VincenzoHDR/Placchetta-AM100/Placchetta Finita/WhatsApp Image 2023-08-04 at 15.59.29.jpeg

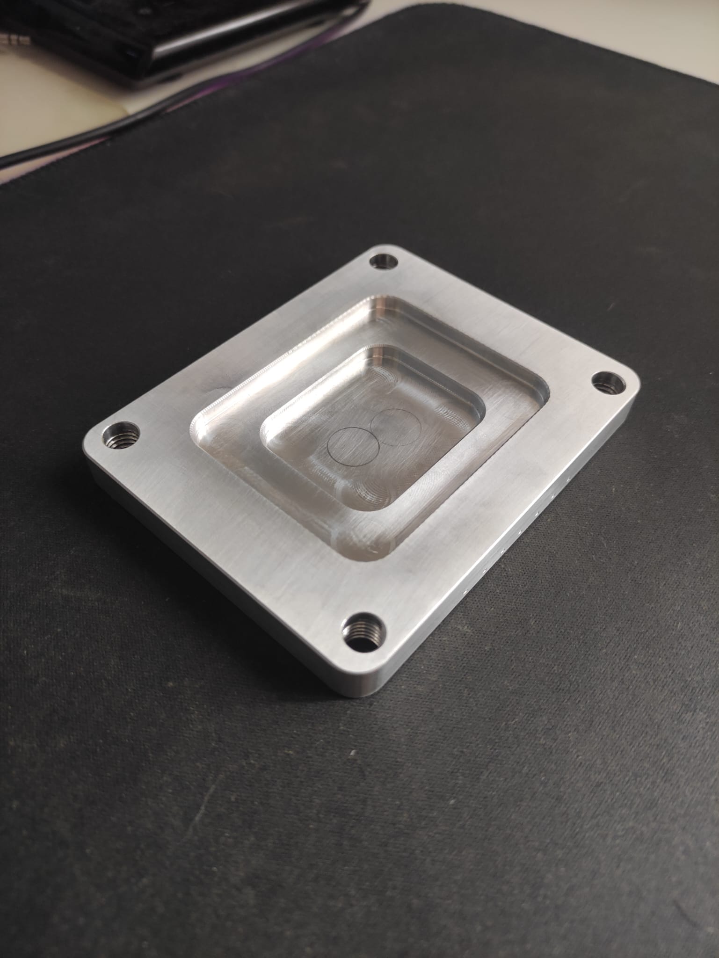
Placchetta Finita/WhatsApp Image 2023-08-04 at 15.59.29.jpeg
